MiniPic/Sunstrip_White_LED/CAO/GDSTIME 50mm x 50mm x 20mm 12V Brushless Cooling Fan.stp

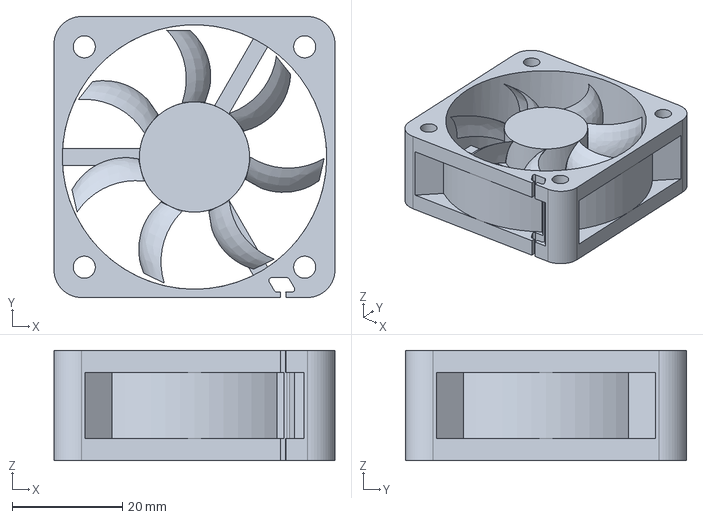
[picture p18: CAD file, 2020-05-09]
CAO/GDSTIME 50mm x 50mm x 20mm 12V Brushless Cooling Fan.stp
51.0 x 51.0 x 20.0 mm
