MiniPic/Sunstrip_White_LED/CAO/Neutrik NC3FAH2.stp.SLDPRT

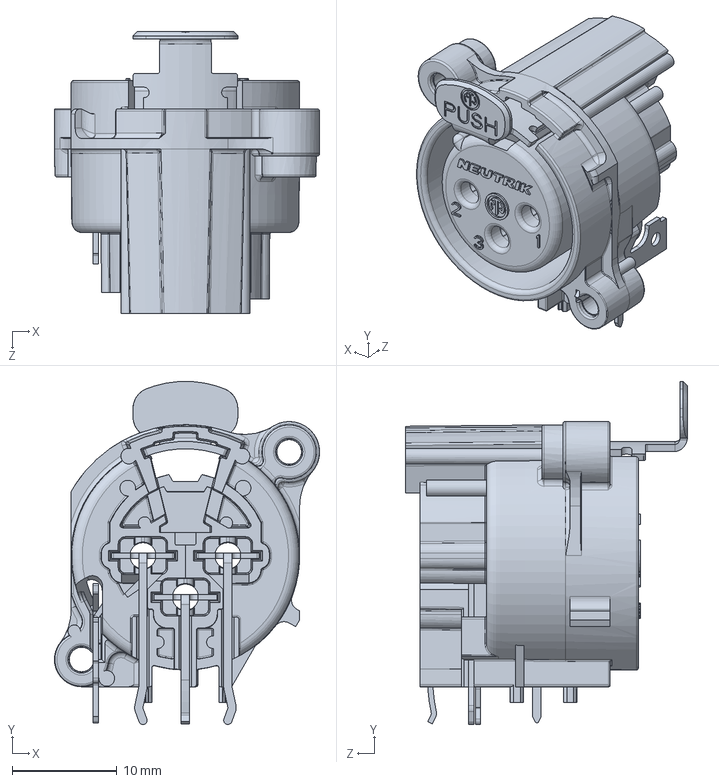
[picture p19: CAD file, 2020-05-09]
CAO/Neutrik NC3FAH2.stp.SLDPRT
25.3 x 32.7 x 26.9 mm
