MiniPic/Sunstrip_White_LED/CAO/socket head cap screw_iso.SLDPRT

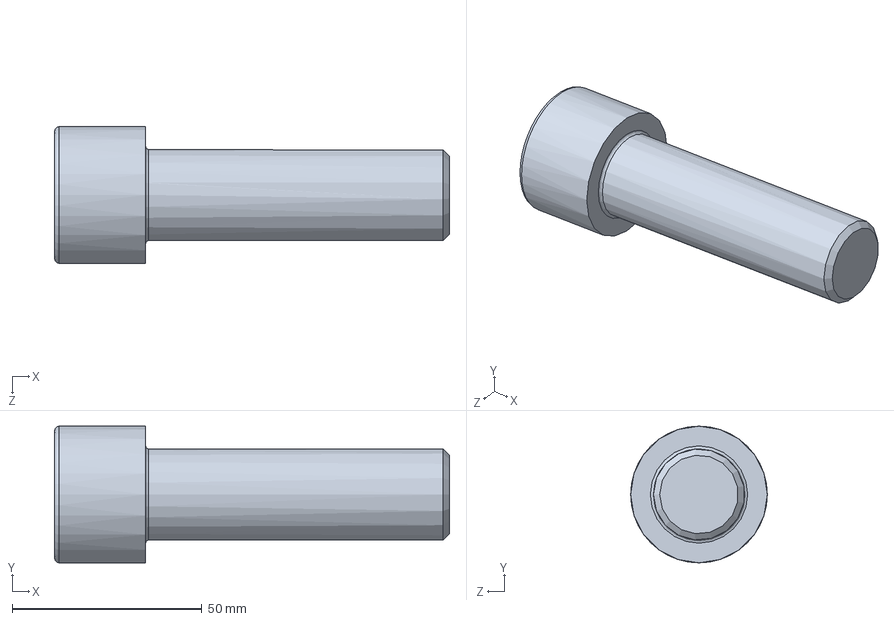
[picture p20: CAD file, 2020-05-09]
CAO/socket head cap screw_iso.SLDPRT
104.0 x 36.0 x 36.0 mm
